MisterStump/Dice-Puck/Dice Images/2 - png/D4.png

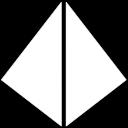
Dice Images/2 - png/D4.png
