MisterStump/Dice-Puck/Dice Images/2 - png/D6.png

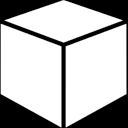
Dice Images/2 - png/D6.png
