MisterStump/Dice-Puck/Dice Images/2 - png/D8.png

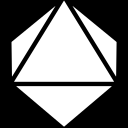
Dice Images/2 - png/D8.png
