MisterStump/Dice-Puck/Dice Images/2 - png/D10.png

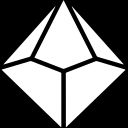
Dice Images/2 - png/D10.png
