MisterStump/Dice-Puck/Dice Images/2 - png/D12.png

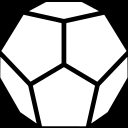
Dice Images/2 - png/D12.png
