MisterStump/Dice-Puck/Dice Images/2 - png/D20.png

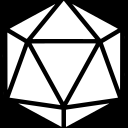
Dice Images/2 - png/D20.png
