MisterStump/Dice-Puck/Dice Images/2 - png/D100.png

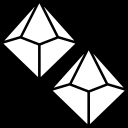
Dice Images/2 - png/D100.png
